fengzhe-li/stm32-fall-detection-system/docs/images/Alert SMS received when body temperature exceeds the threshold.jpg

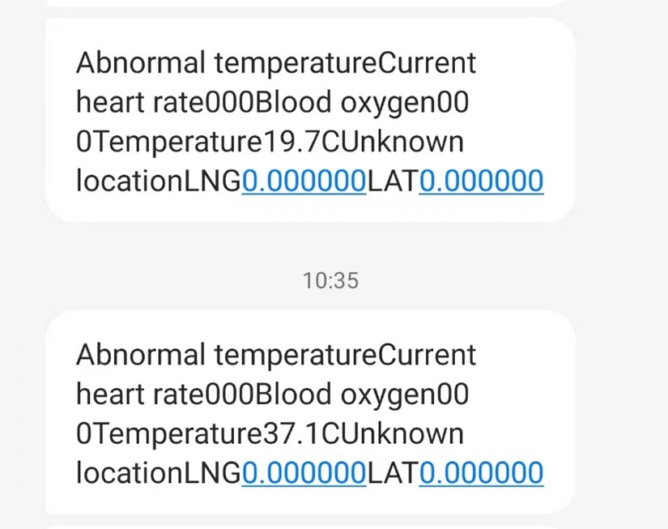
docs/images/Alert SMS received when body temperature exceeds the threshold.jpg
